nilseuropa/hx20_rom_cart/src/ftp.h

#ifndef FTP_ROUTINES_H_
#define FTP_ROUTINES_H_

FtpServer ftpSrv;

void _callback(FtpOperation ftpOperation, unsigned int freeSpace, unsigned int totalSpace){
  switch (ftpOperation) {
    case FTP_CONNECT:
      Serial.println(F("FTP: Connected!"));
      break;
    case FTP_DISCONNECT:
      Serial.println(F("FTP: Disconnected!"));
      break;
    case FTP_FREE_SPACE_CHANGE:
      Serial.printf("FTP: Free space change, free %u of %u!\n", freeSpace, totalSpace);
      break;
    default:
      break;
  }
};

void _transferCallback(FtpTransferOperation ftpOperation, const char* name, unsigned int transferredSize){
  switch (ftpOperation) {
    case FTP_UPLOAD_START:
      Serial.println(F("FTP: Upload start!"));
      break;
    case FTP_UPLOAD:
      Serial.printf("FTP: Upload of file %s byte %u\n", name, transferredSize);
      break;
    case FTP_TRANSFER_STOP:
      Serial.println(F("FTP: Finish transfer!"));
      break;
    case FTP_TRANSFER_ERROR:
      Serial.println(F("FTP: Transfer error!"));
      break;
    default:
      break;
  }
};

void initFTP(const char * ssid, const char * password){
  WiFi.begin(ssid, password);
  while (WiFi.status() != WL_CONNECTED) // Wait for connection
  {
    delay(500);
    Serial.printf_P(PSTR("."));
    // TODO: give up
  }
  Serial.printf_P(PSTR("\nConnected to %s, IP address is %s\r\n"), ssid, WiFi.localIP().toString().c_str());
  ftpSrv.begin("user","password");
}

#endif
